Armastardo/PaneledOpenRectangle/PCB/OpenRectangle.kicad_sch

## KiCad design PCB/OpenRectangle.kicad_sch (2023-03-07)

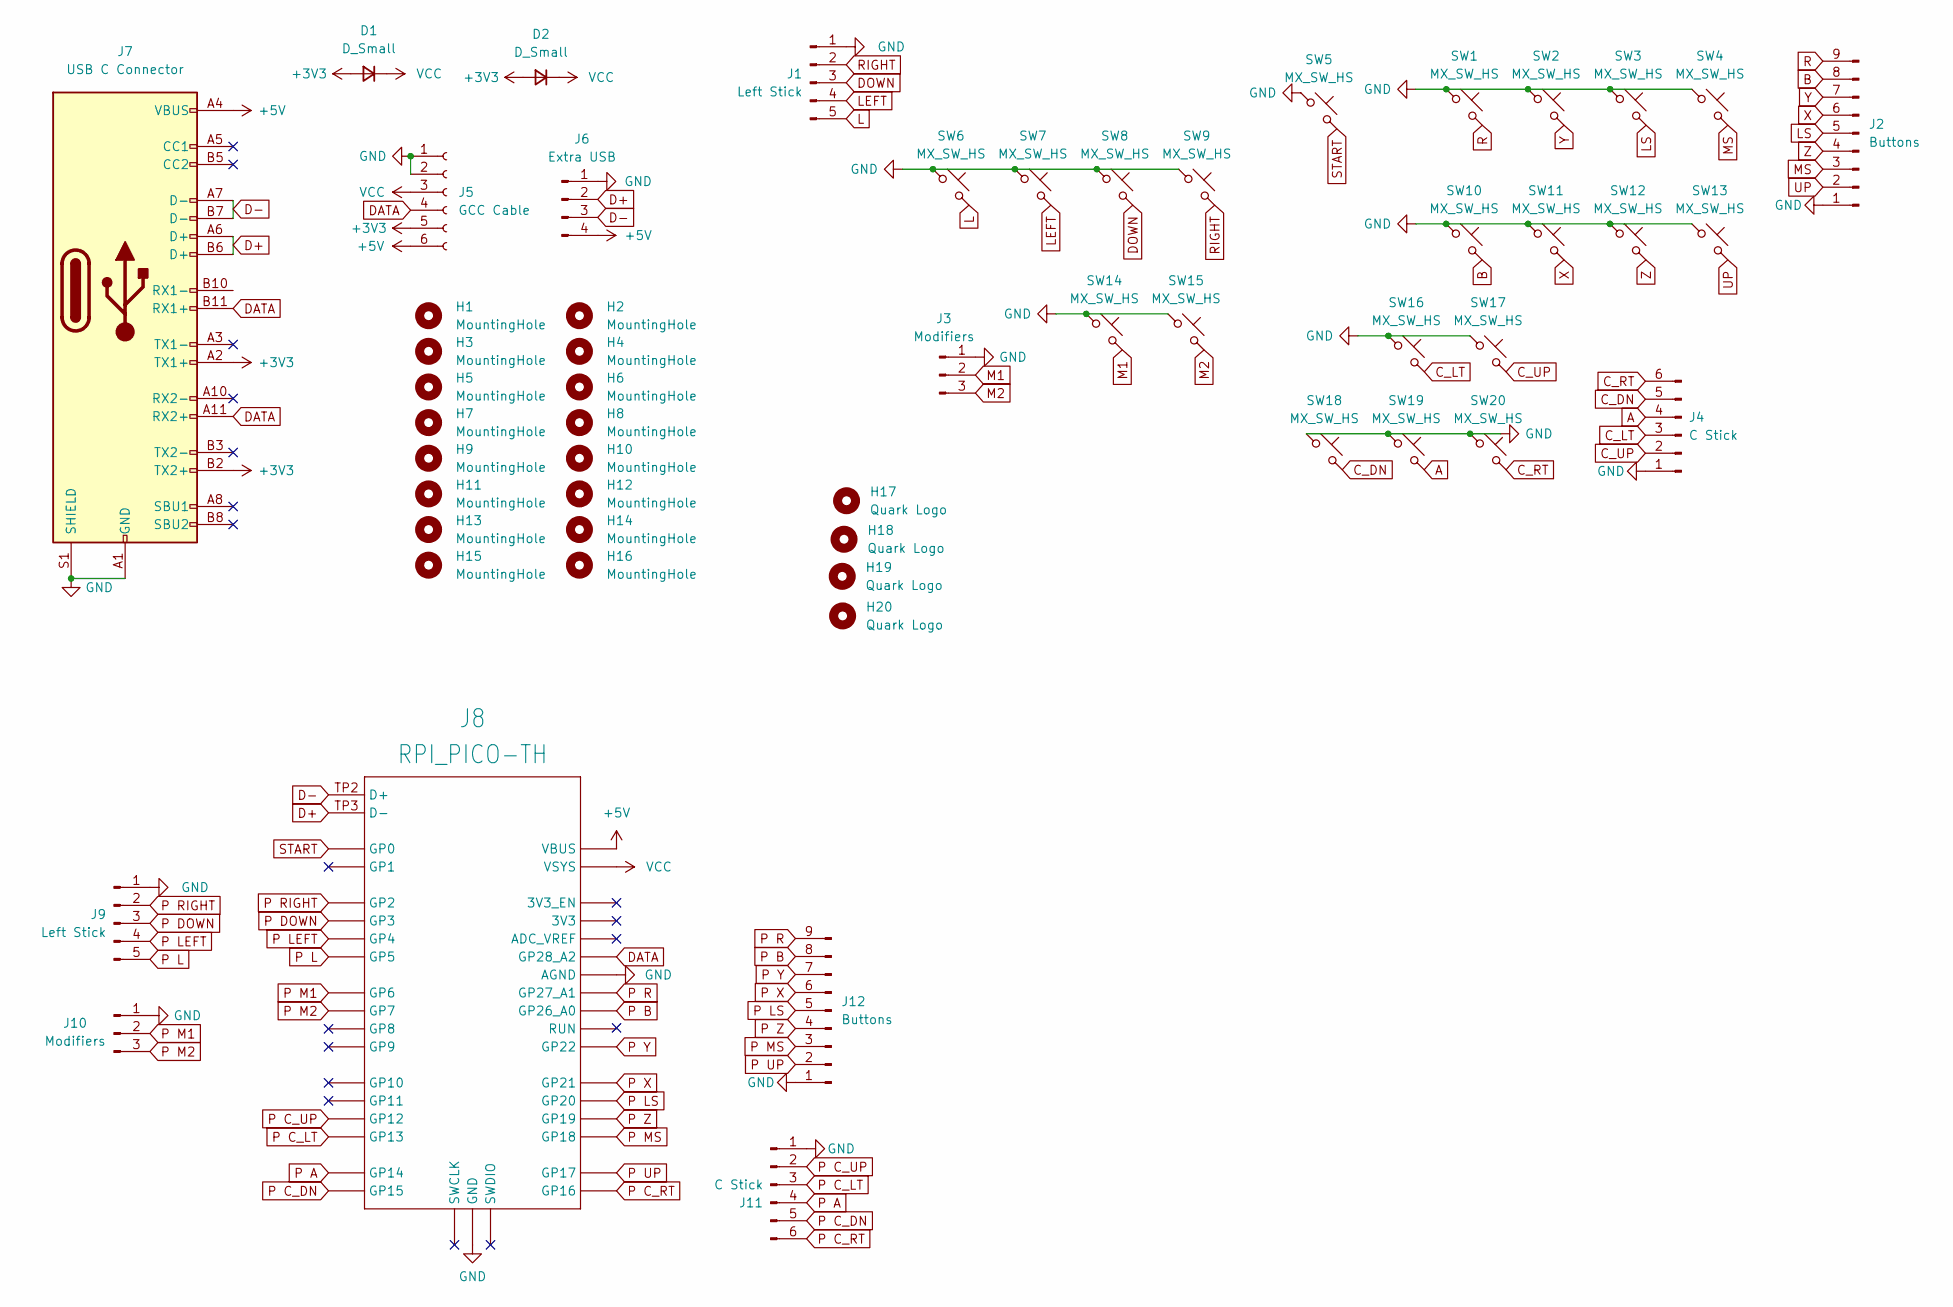
[picture p6: schematic OpenRectangle.kicad_sch]

Parts:
D1: D_Small; D_DO-41_SOD81_P10.16mm_Horizontal
D2: D_Small; D_SOD-123
H1, H2, H3, H4, H5, H6, H7, H8, H9, H10, H11, H12, H13, H14, H15, H16: MountingHole; MountingHole_2.2mm_M2_DIN965
H17, H18, H19, H20: Quark Logo; qw new logo silk + copper md
J1, J9: Left Stick; PinHeader_1x05_P2.54mm_Vertical
J2, J12: Buttons; PinHeader_1x09_P2.54mm_Vertical
J3, J10: Modifiers; PinHeader_1x03_P2.54mm_Vertical
J4, J11: C Stick; PinHeader_1x06_P2.54mm_Vertical
J5: GCC Cable; PinHeader_1x06_P2.54mm_Vertical
J6: Extra USB; PinHeader_1x04_P2.54mm_Vertical
J7: USB C Connector; TYPE-C_24P_QCHT
J8: RPI_PICO-TH; RPI_PICO_TH
SW1, SW2, SW3, SW4, SW5, SW6, SW7, SW8, SW9, SW10, SW11, SW12, SW13, SW14, SW15, SW16, SW17, SW18, SW19, SW20: MX_SW_HS; SW_MX_HS_1u

Connections:
+3V3: D1.2 (A), D2.2 (A), J5.5, J7.A2 (TX1+), J7.B2 (TX2+)
+5V: J5.6, J6.4, J7.A4 (VBUS), J7.A9 (VBUS), J7.B4 (VBUS), J7.B9 (VBUS), J8.VBUS
A: J4.4, SW19.2
B: J2.8, SW10.2
C_DN: J4.5, SW18.2
C_LT: J4.3, SW16.2
C_RT: J4.6, SW20.2
C_UP: J4.2, SW17.2
D+: J6.2, J7.A6 (D+), J7.B6 (D+), J8.TP3 (D-)
D-: J6.3, J7.A7 (D-), J7.B7 (D-), J8.TP2 (D+)
DATA: J5.4, J7.A11 (RX2+), J7.B11 (RX1+), J8.GP28_A2
DOWN: J1.3, SW8.2
GND: J1.1, J2.1, J3.1, J4.1, J5.1, J5.2, J6.1, J7.A1 (GND), J7.A12 (GND), J7.B1 (GND), J7.B12 (GND), J7.S1 (SHIELD), J8.AGND, J8.GND@1 (GND), J8.GND@2 (GND), J8.GND@3 (GND), J8.GND@4 (GND), J8.GND@5 (GND), J8.GND@6 (GND), J8.GND@7 (GND), J8.GND@8 (GND), J9.1, J10.1, J11.1, J12.1, SW1.1, SW2.1, SW3.1, SW4.1, SW5.1, SW6.1, SW7.1, SW8.1, SW9.1, SW10.1, SW11.1, SW12.1, SW13.1, SW14.1, SW15.1, SW16.1, SW17.1, SW18.1, SW19.1, SW20.1
L: J1.5, SW6.2
LEFT: J1.4, SW7.2
LS: J2.5, SW3.2
M1: J3.2, SW14.2
M2: J3.3, SW15.2
MS: J2.3, SW4.2
P A: J8.GP14, J11.4
P B: J8.GP26_A0, J12.8
P C_DN: J8.GP15, J11.5
P C_LT: J8.GP13, J11.3
P C_RT: J8.GP16, J11.6
P C_UP: J8.GP12, J11.2
P DOWN: J8.GP3, J9.3
P L: J8.GP5, J9.5
P LEFT: J8.GP4, J9.4
P LS: J8.GP20, J12.5
P M1: J8.GP6, J10.2
P M2: J8.GP7, J10.3
P MS: J8.GP18, J12.3
P R: J8.GP27_A1, J12.9
P RIGHT: J8.GP2, J9.2
P UP: J8.GP17, J12.2
P X: J8.GP21, J12.6
P Y: J8.GP22, J12.7
P Z: J8.GP19, J12.4
R: J2.9, SW1.2
RIGHT: J1.2, SW9.2
START: J8.GP0, SW5.2
UP: J2.2, SW13.2
VCC: D1.1 (K), D2.1 (K), J5.3, J8.VSYS
X: J2.6, SW11.2
Y: J2.7, SW2.2
Z: J2.4, SW12.2
